VicRattlehead502/Medicine-Man/ivelina-design/sketches/not-logged.jpg

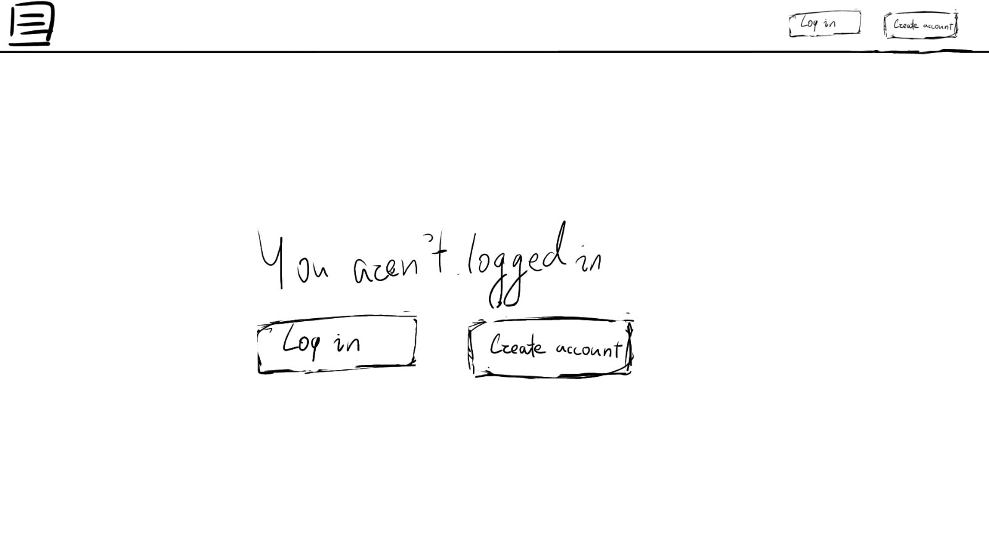
ivelina-design/sketches/not-logged.jpg
