VicRattlehead502/Medicine-Man/ivelina-design/sketches/sound-page.jpg

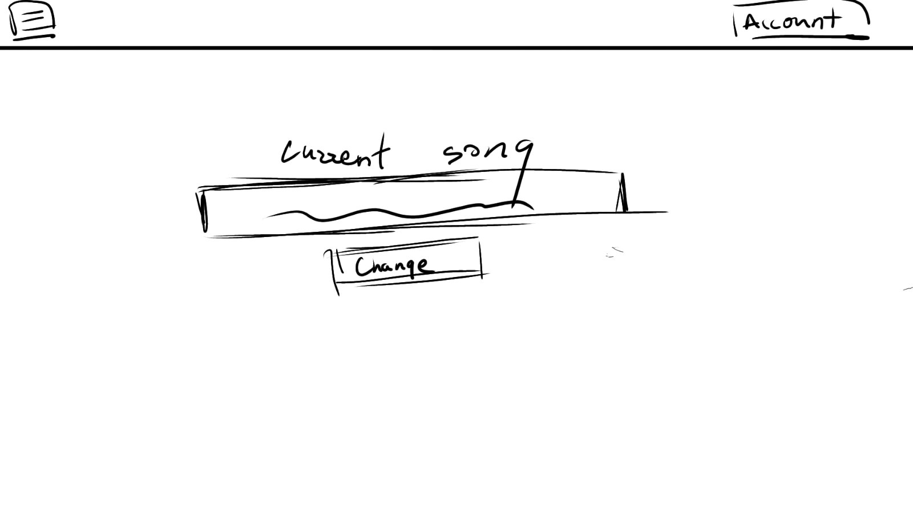
ivelina-design/sketches/sound-page.jpg
