VicRattlehead502/Medicine-Man/other/config.png

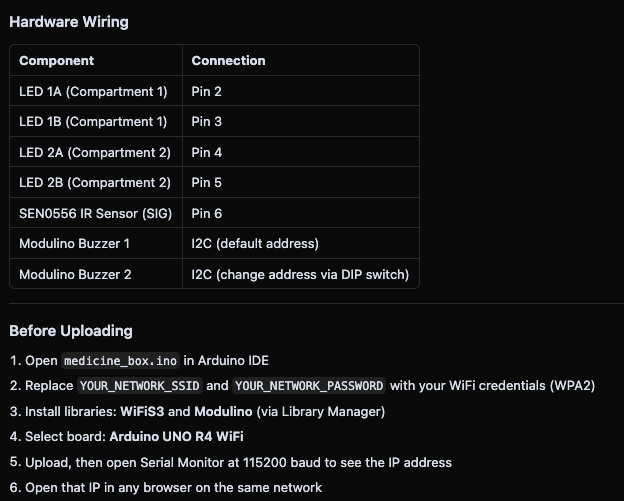
other/config.png
