VicRattlehead502/Medicine-Man/Medicine_Man_Schematic/Medicine_Man/Medicine_Man/Medicine_Man.kicad_sch

## KiCad design Medicine_Man_Schematic/Medicine_Man/Medicine_Man/Medicine_Man.kicad_sch (2026-03-27)

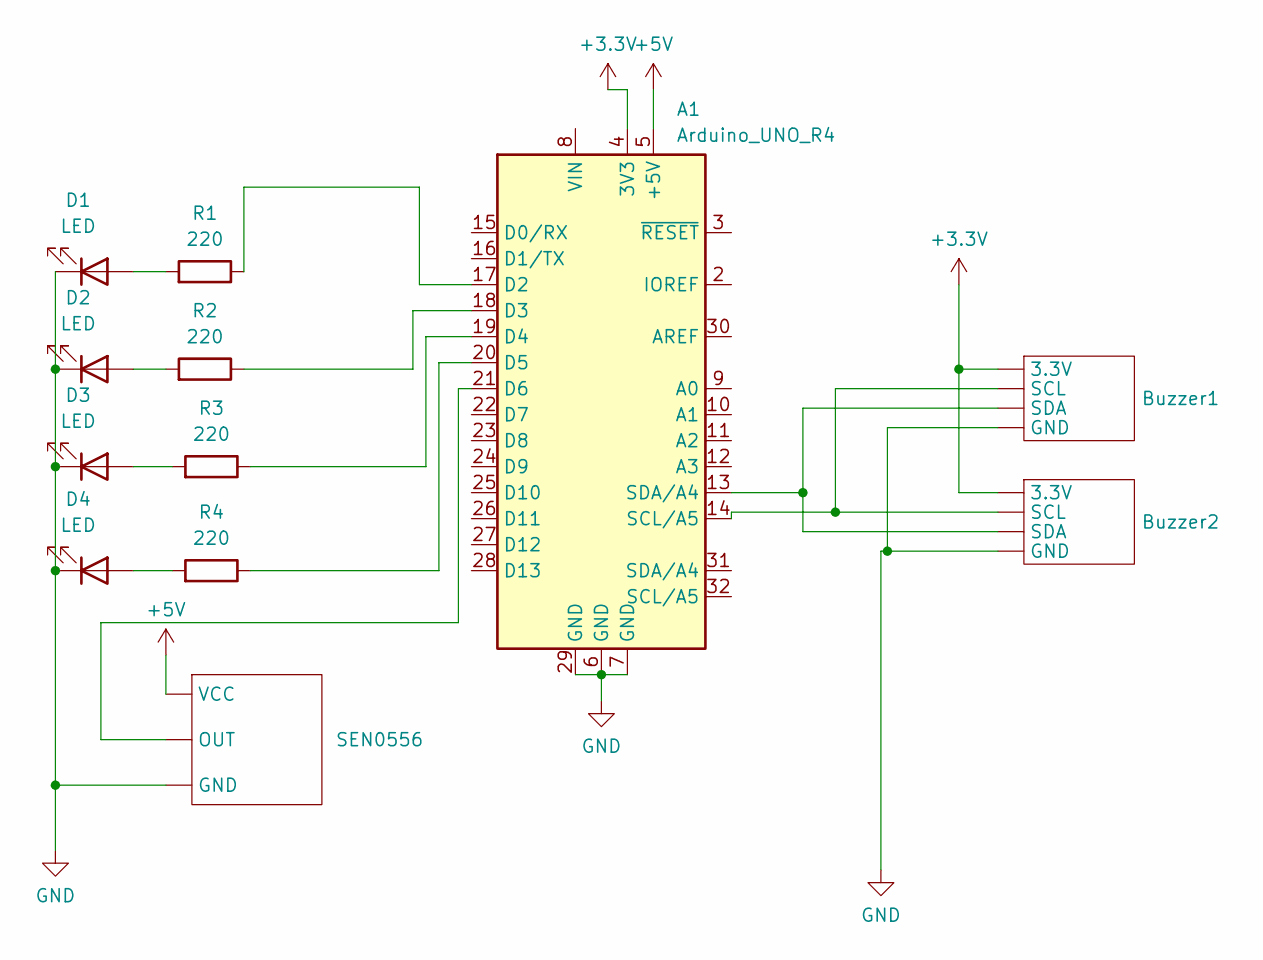
[picture p23: schematic Medicine_Man.kicad_sch]

Parts:
A1: Arduino_UNO_R4; Arduino_UNO_R3
Buzzer1, Buzzer2: (no value)
D1, D2, D3, D4: LED
R1, R2, R3, R4: 220
SEN0556: (no value)

Connections:
+3.3V: A1.4 (3V3), Buzzer1., Buzzer2.
+5V: A1.5 (+5V), SEN0556.
GND: A1.6 (GND), A1.7 (GND), A1.29 (GND), Buzzer1., Buzzer2., D1.1 (K), D2.1 (K), D3.1 (K), D4.1 (K), SEN0556.
unnamed: A1.13 (SDA/A4), Buzzer1., Buzzer2.
unnamed: A1.14 (SCL/A5), Buzzer1., Buzzer2.
unnamed: A1.17 (D2), R1.1
unnamed: A1.18 (D3), R2.1
unnamed: A1.19 (D4), R3.1
unnamed: A1.20 (D5), R4.1
unnamed: A1.21 (D6), SEN0556.
unnamed: D1.2 (A), R1.2
unnamed: D2.2 (A), R2.2
unnamed: D3.2 (A), R3.2
unnamed: D4.2 (A), R4.2
