VicRattlehead502/Medicine-Man/other/instructions.png

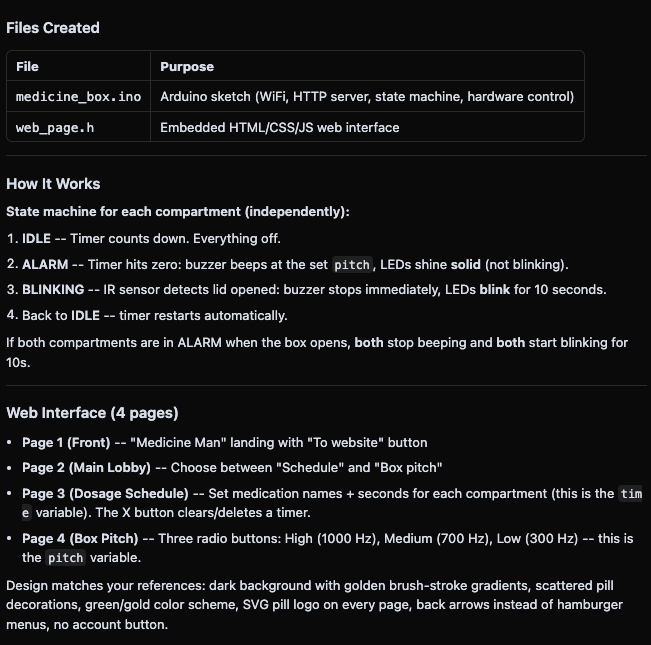
other/instructions.png
